Monsieur-Machine/main_robot_2025-2026/program/motion_controller/src/headers/robot.h

#ifndef ROBOT_H
#define ROBOT_H

#include "i2c/headers/i2c_slave.h"

typedef struct robot_t {
    i2c_buffer_t i2c_buffer;

    bool is_running;
    float delta_time_ms;
} robot_t;

extern robot_t robot;

// Init all robot's components
void robot_init(void);
// Handle inputs and outputs
void robot_update(void);
// Deinit all robot's components
void robot_deinit(void);

#endif // ROBOT_H
